ARTSAT/MorikawaSDK/Arduino/hardware/mega-pro-3.3V/cores/arduino/wiring_pulse.c

/*
  wiring_pulse.c - pulseIn() function
  Part of Arduino - http://www.arduino.cc/

  Copyright (c) 2005-2006 David A. Mellis

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
  $Id: wiring_pulse.c,v 1.1 2013/11/29 17:05:39 administrator Exp $
*/

#include "wiring_private.h"
#include "pins_arduino.h"

/* Measures the length (in microseconds) of a pulse on the pin; state is HIGH
 * or LOW, the type of pulse to measure.  Works on pulses from 2-3 microseconds
 * to 3 minutes in length, but must be called at least a few dozen microseconds
 * before the start of the pulse. */
unsigned long pulseIn(uint8_t pin, uint8_t state, unsigned long timeout)
{
	// cache the port and bit of the pin in order to speed up the
	// pulse width measuring loop and achieve finer resolution.  calling
	// digitalRead() instead yields much coarser resolution.
	uint8_t bit = digitalPinToBitMask(pin);
	uint8_t port = digitalPinToPort(pin);
	uint8_t stateMask = (state ? bit : 0);
	unsigned long width = 0; // keep initialization out of time critical area
	
	// convert the timeout from microseconds to a number of times through
	// the initial loop; it takes 16 clock cycles per iteration.
	unsigned long numloops = 0;
	unsigned long maxloops = microsecondsToClockCycles(timeout) / 16;
	
	// wait for any previous pulse to end
	while ((*portInputRegister(port) & bit) == stateMask)
		if (numloops++ == maxloops)
			return 0;
	
	// wait for the pulse to start
	while ((*portInputRegister(port) & bit) != stateMask)
		if (numloops++ == maxloops)
			return 0;
	
	// wait for the pulse to stop
	while ((*portInputRegister(port) & bit) == stateMask) {
		if (numloops++ == maxloops)
			return 0;
		width++;
	}

	// convert the reading to microseconds. The loop has been determined
	// to be 20 clock cycles long and have about 16 clocks between the edge
	// and the start of the loop. There will be some error introduced by
	// the interrupt handlers.
	return clockCyclesToMicroseconds(width * 21 + 16); 
}
